partyrobotics/bartendro/firmware/common/pack7.h

#ifndef __PACK7_H__
#define __PACK7_H__

void pack_7bit(uint8_t in_count, uint8_t *in, uint8_t *out_count, uint8_t *out);
void unpack_7bit(uint8_t in_count, uint8_t *in, uint8_t *out_count, uint8_t *out);

#endif
