partyrobotics/bartendro/ui/bartendro/router/status_led.py

#!/usr/bin/env python

import sys
import logging
from time import sleep
try:
    import RPi.GPIO as gpio
    gpio_missing = 0
except ImportError, e:
    if e.message != 'No module named RPi.GPIO':
        raise
    gpio_missing = 1

log= logging.getLogger('bartendro')

class StatusLED(object):

    # pin definitions
    red = 18
    green = 16
    blue = 22

    def __init__(self, software_only):
        self.software_only = software_only
        if self.software_only: return

        if gpio_missing:
            loglogerror("You must install the RPi.GPIO module")
            sys.exit(-1)

        # select the method by which we want to identify GPIO pins
        gpio.setmode(gpio.BOARD)

        # set our gpio pins to OUTPUT
        gpio.setup(self.red, gpio.OUT)
        gpio.setup(self.green, gpio.OUT)
        gpio.setup(self.blue, gpio.OUT)

    def swap_blue_green(self):
        self.green = 22
        self.blue = 16

    def set_color(self, red, green, blue):
        if self.software_only: return
        if red:
            gpio.output(self.red, gpio.HIGH)
        else:
            gpio.output(self.red, gpio.LOW)
            
        if green:
            gpio.output(self.green, gpio.HIGH)
        else:
            gpio.output(self.green, gpio.LOW)

        if blue:
            gpio.output(self.blue, gpio.HIGH)
        else:
            gpio.output(self.blue, gpio.LOW)
